Ldalvik/C2000-WordClock/main.h

/*
   Copyright (c) 2014-2020 by Plexim GmbH
   All rights reserved.

   A free license is granted to anyone to use this software for any legal
   non safety-critical purpose, including commercial applications, provided
   that:
   1) IT IS NOT USED TO DIRECTLY OR INDIRECTLY COMPETE WITH PLEXIM, and
   2) THIS COPYRIGHT NOTICE IS PRESERVED in its entirety.

   THE SOFTWARE IS PROVIDED "AS IS", WITHOUT WARRANTY OF ANY KIND, EXPRESS
   OR IMPLIED, INCLUDING BUT NOT LIMITED TO THE WARRANTIES OF MERCHANTABILITY,
   FITNESS FOR A PARTICULAR PURPOSE AND NONINFRINGEMENT. IN NO EVENT SHALL THE
   AUTHORS OR COPYRIGHT HOLDERS BE LIABLE FOR ANY CLAIM, DAMAGES OR OTHER
   LIABILITY, WHETHER IN AN ACTION OF CONTRACT, TORT OR OTHERWISE, ARISING FROM,
   OUT OF OR IN CONNECTION WITH THE SOFTWARE OR THE USE OR OTHER DEALINGS IN THE
   SOFTWARE.
 */

#ifndef MAIN_H_
#define MAIN_H_

#endif // MAIN_H
